LEDswarm/enclosure/mcu.scad

// ESP32-C3 Microcontroller Unit (MCU) 3D Model

board_length = 0.0;
board_width = 0.0;
pcb_thickness = 0.0;
