LEDswarm/enclosure/src/diffusor.scad

// Mockup of the satinized acrylic diffusor tubes.

// Diffusor tube
translate([0, 0, controller_height + 20])
color([0.7, 0.7, 0.7])
ring(40, 34, 40);
